eljeko/Parametric-OpenScad-movement-tray-generator/empty_4_walls.png

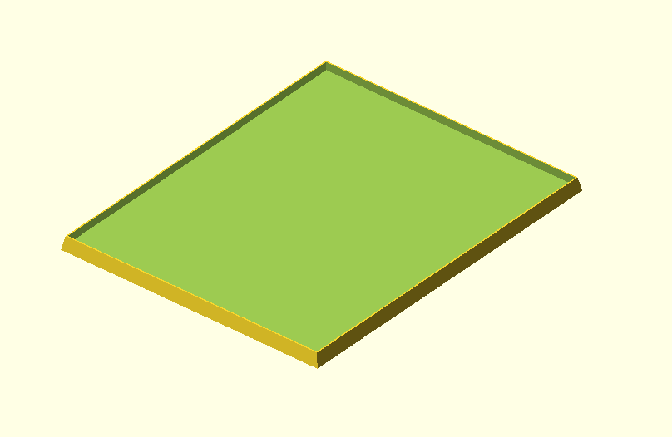
empty_4_walls.png
