eljeko/Parametric-OpenScad-movement-tray-generator/empty_lance_4_walls.png

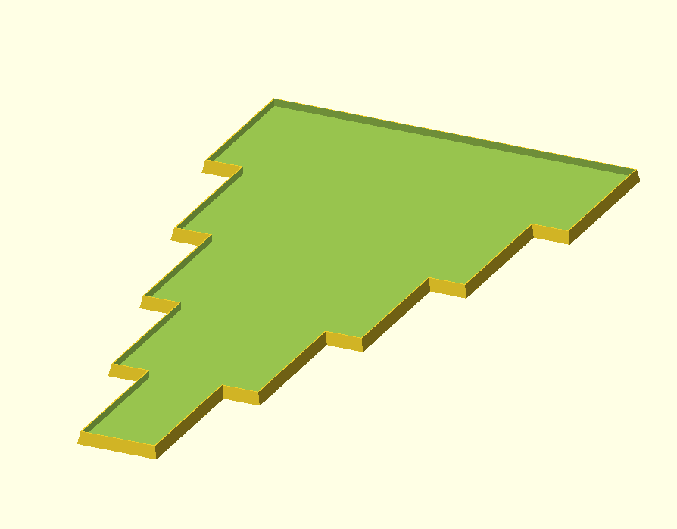
empty_lance_4_walls.png
