eljeko/Parametric-OpenScad-movement-tray-generator/holed.png

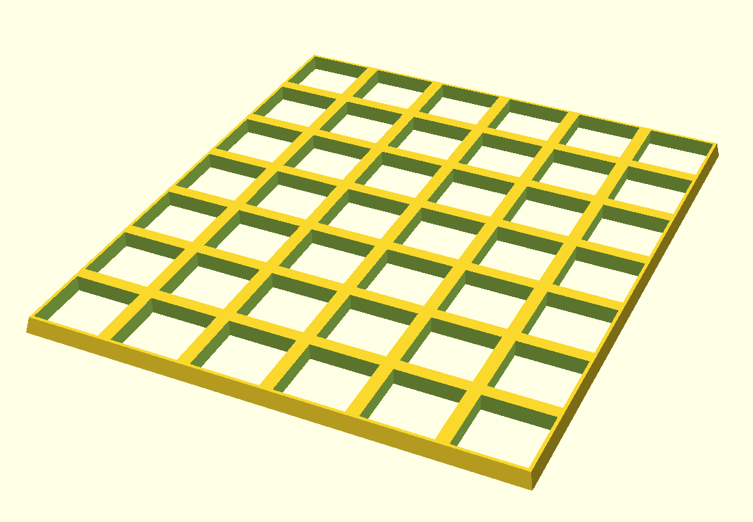
holed.png
