eljeko/Parametric-OpenScad-movement-tray-generator/lower_magnets_5.png

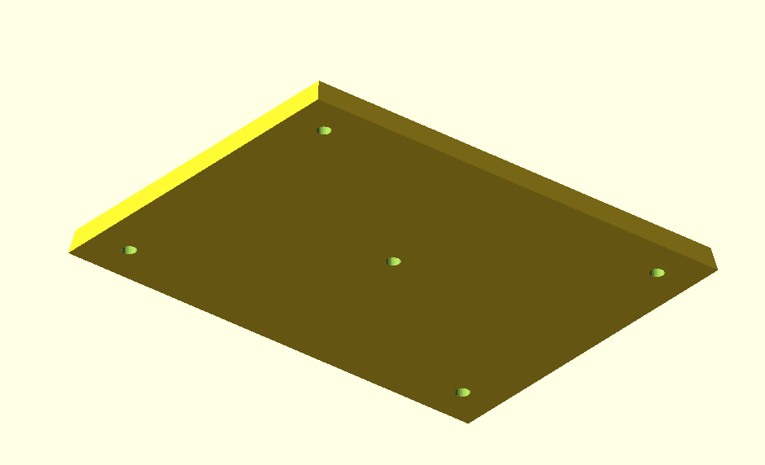
lower_magnets_5.png
