eljeko/Parametric-OpenScad-movement-tray-generator/magnets.png

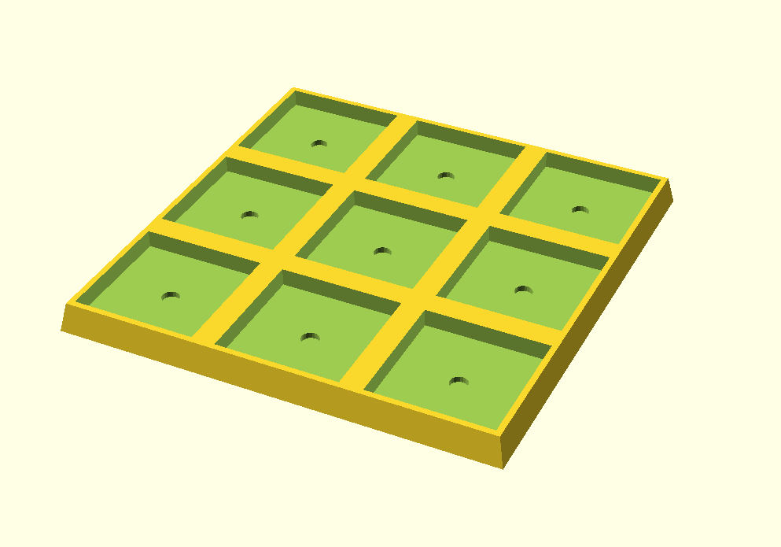
magnets.png
