eljeko/Parametric-OpenScad-movement-tray-generator/main-round.png

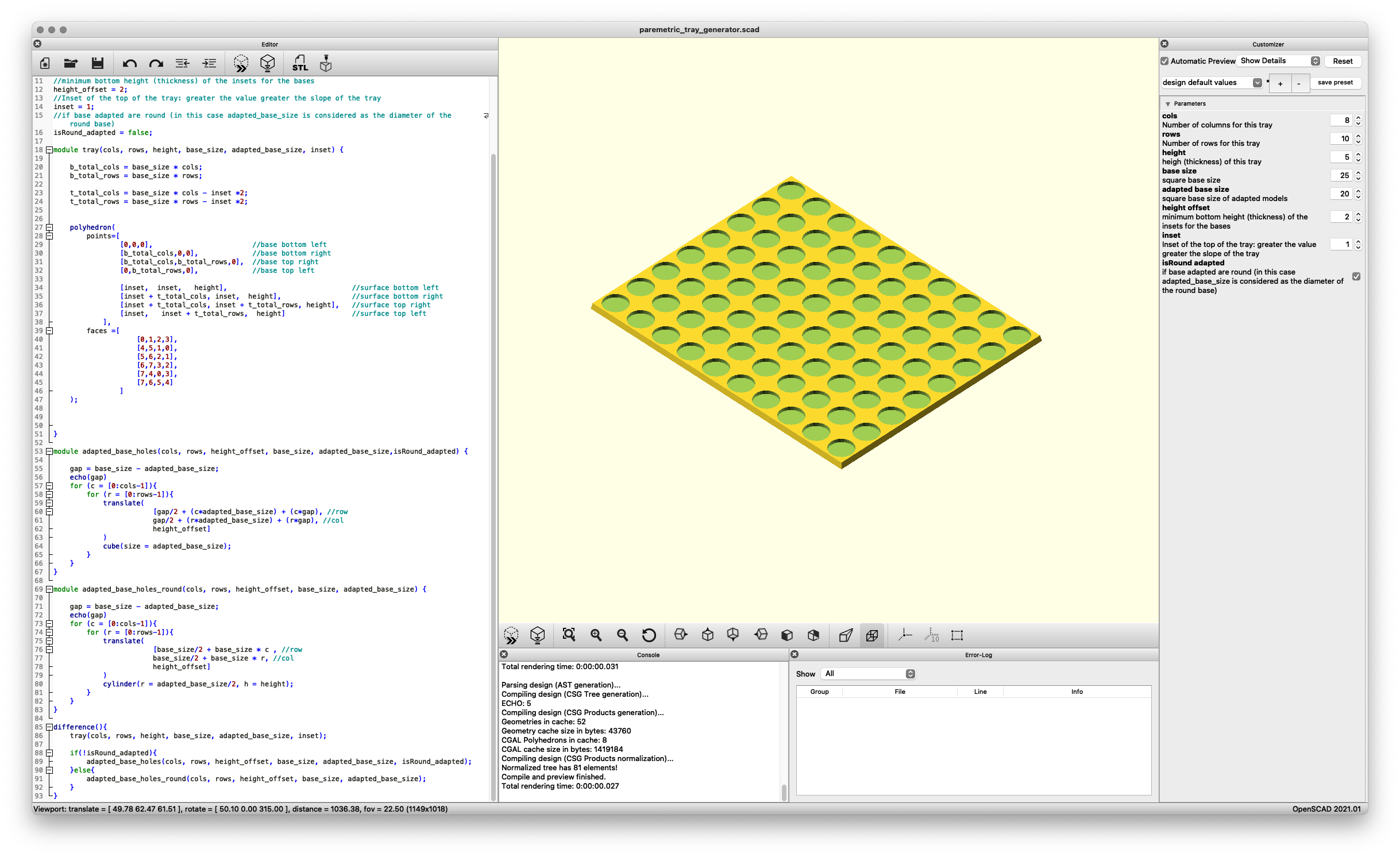
main-round.png
