eljeko/Parametric-OpenScad-movement-tray-generator/main_round_02.png

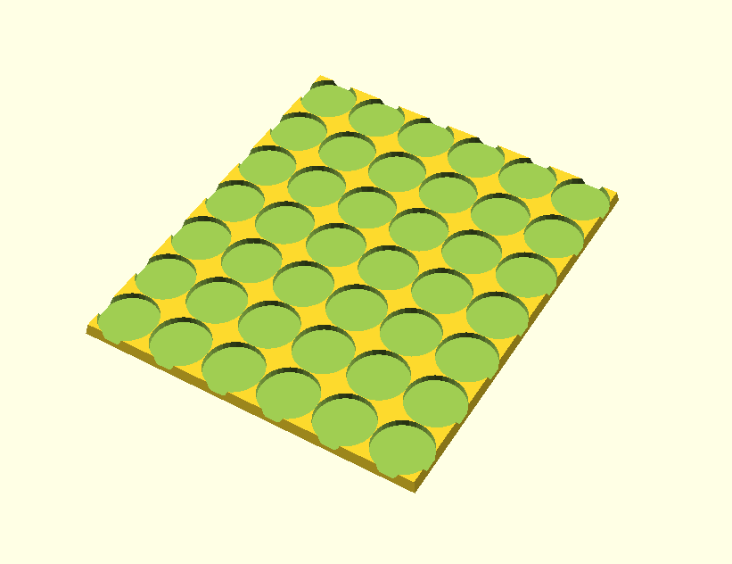
main_round_02.png
