eljeko/Parametric-OpenScad-movement-tray-generator/marked_base.png

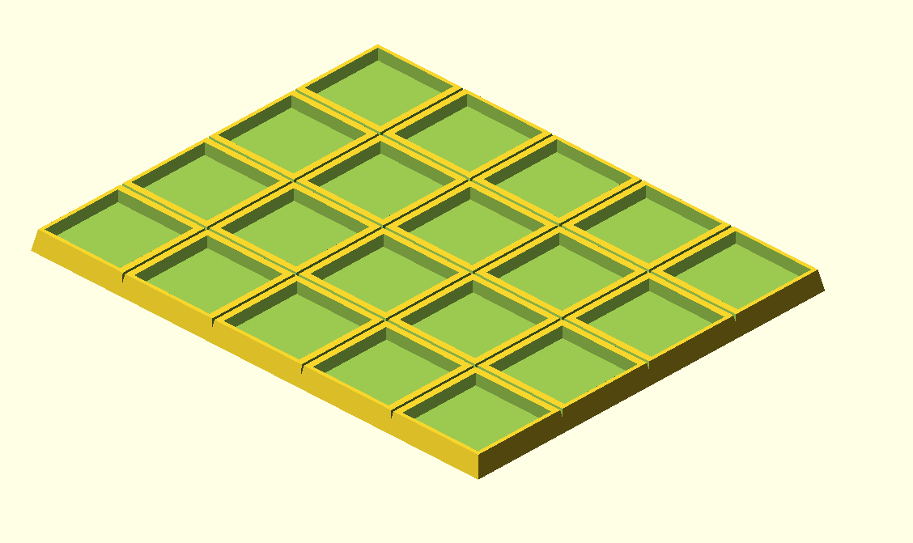
marked_base.png
