eljeko/Parametric-OpenScad-movement-tray-generator/profiles.png

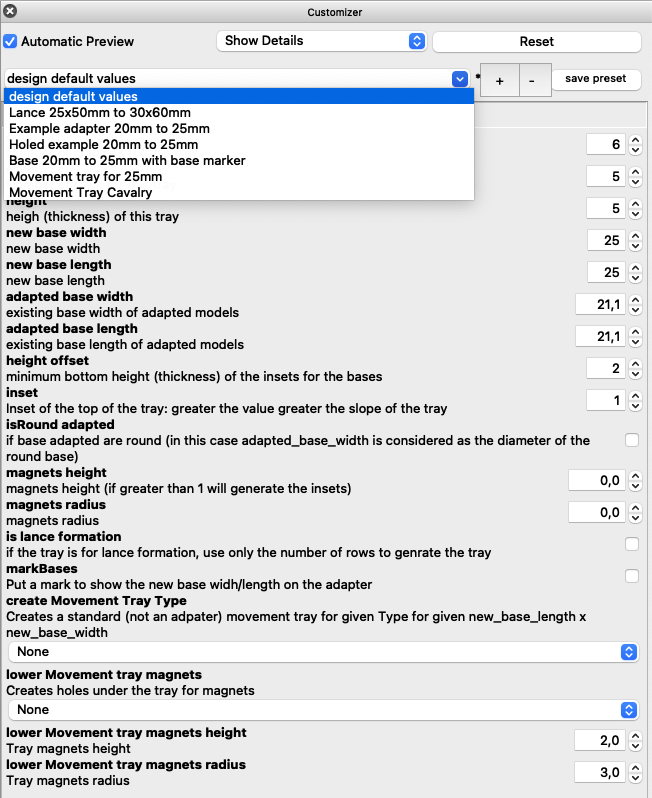
profiles.png
