eljeko/Parametric-OpenScad-movement-tray-generator/rectangular.png

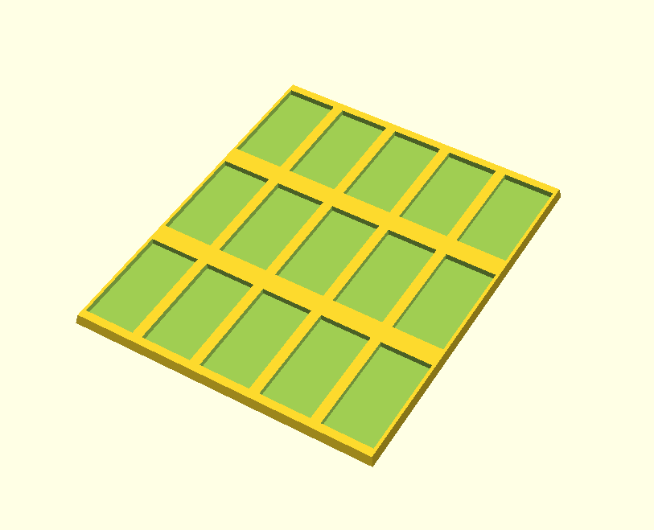
rectangular.png
